ahmed-nazir/Capstone/docs/Design/SystDesign/Electrical_Schematic.png

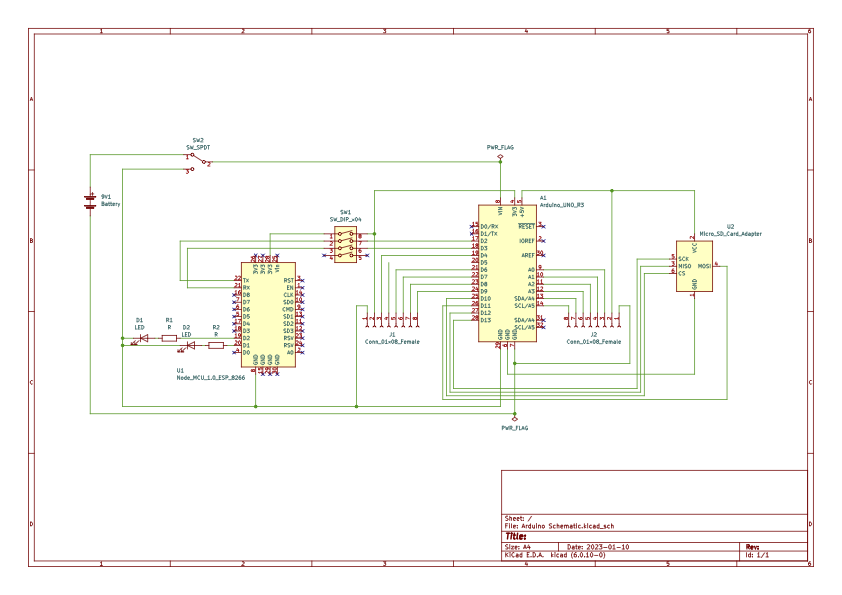
docs/Design/SystDesign/Electrical_Schematic.png
