ahmed-nazir/Capstone/docs/Design/SystDesign/GUI_designer.png

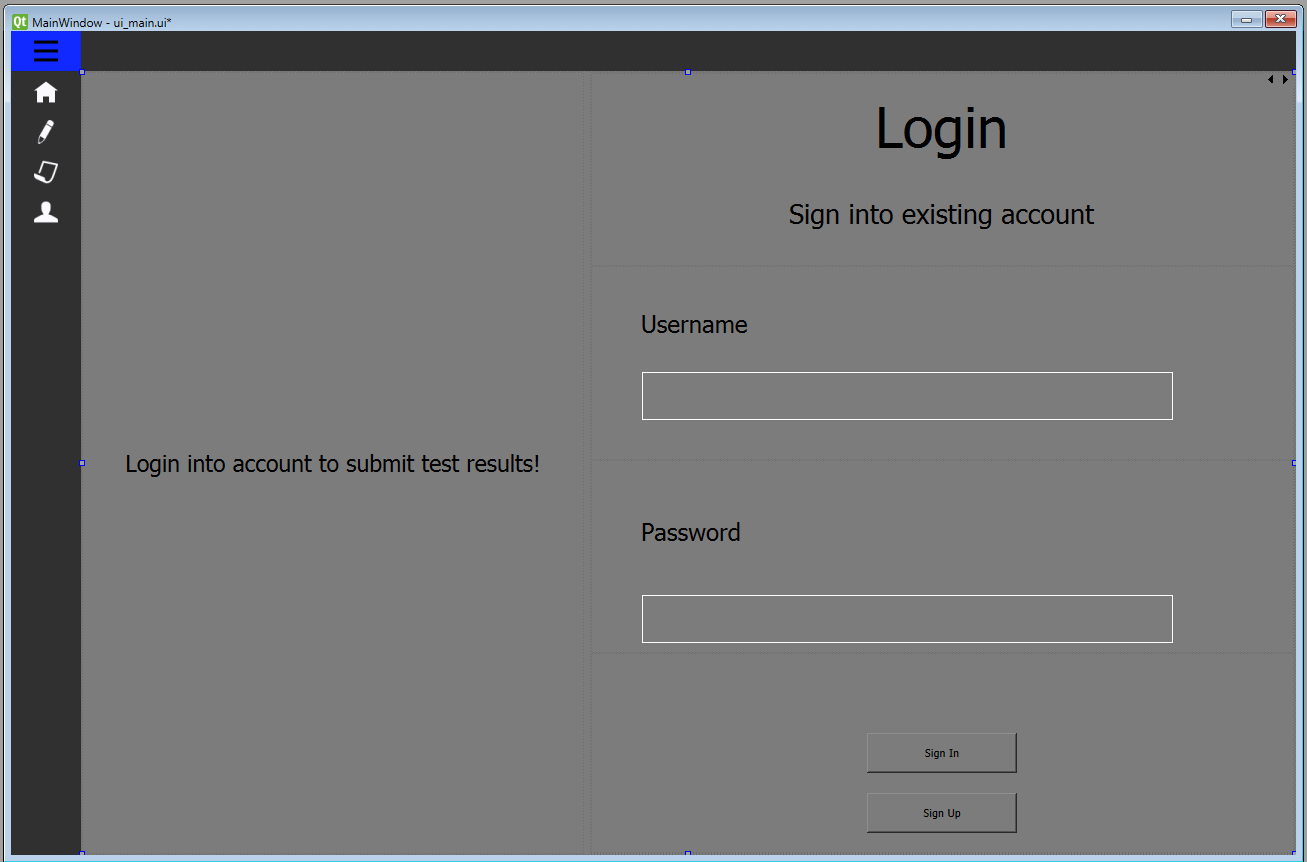
docs/Design/SystDesign/GUI_designer.png
