ahmed-nazir/Capstone/docs/Design/SystDesign/GUI_sketch.png

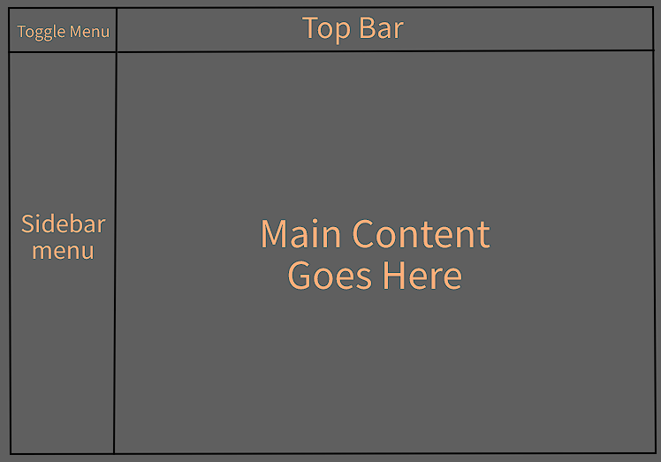
docs/Design/SystDesign/GUI_sketch.png
