ahmed-nazir/Capstone/docs/Design/SystDesign/PCB_Schematic.png

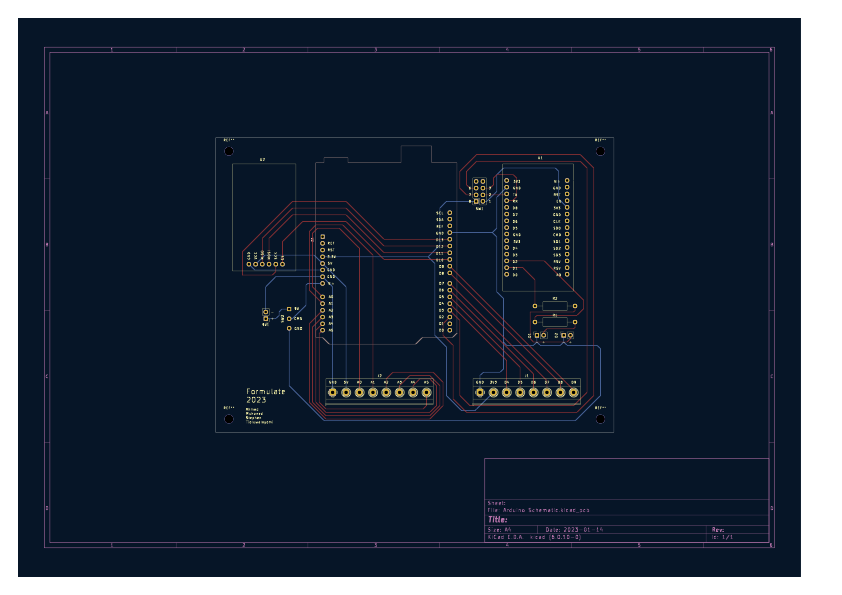
docs/Design/SystDesign/PCB_Schematic.png
