ahmed-nazir/Capstone/docs/SRS/functional_decomposition.png

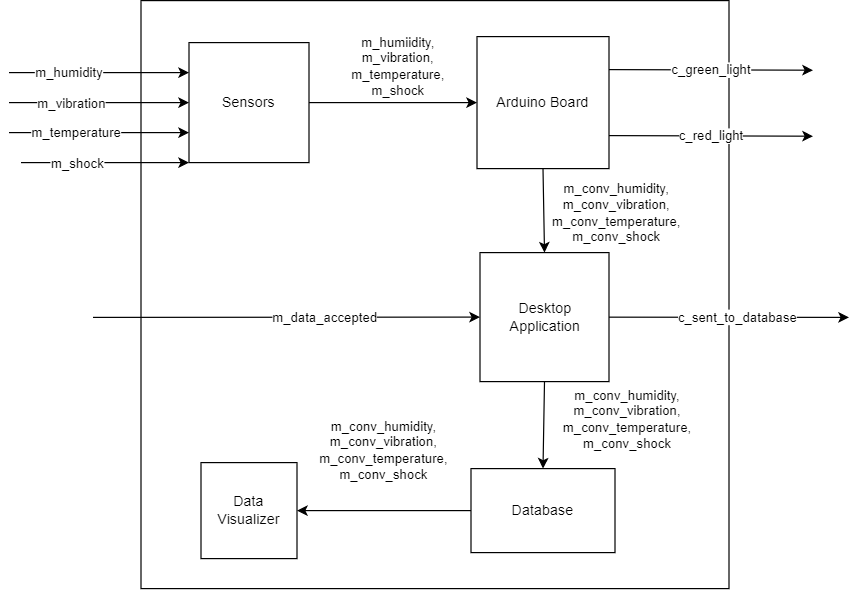
docs/SRS/functional_decomposition.png
