ahmed-nazir/Capstone/docs/VnVReport/Latency_Data.png

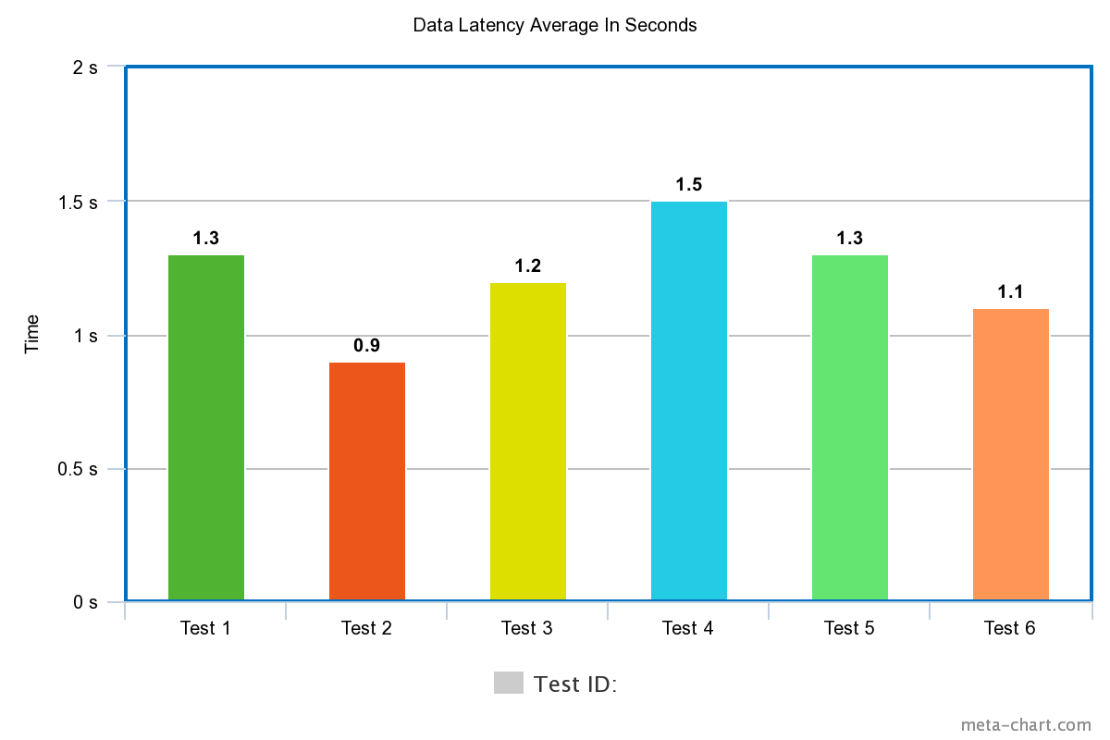
docs/VnVReport/Latency_Data.png
