ahmed-nazir/Capstone/test/Formulate Image.jpg

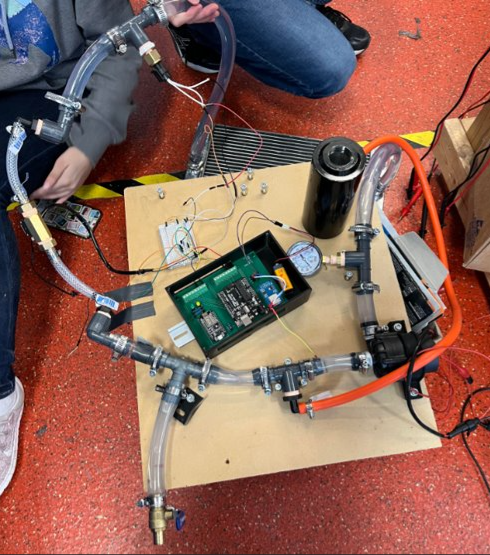
test/Formulate Image.jpg
