ahmed-nazir/Capstone/src/Electrical/REV 0/Electrical Schematic.pdf

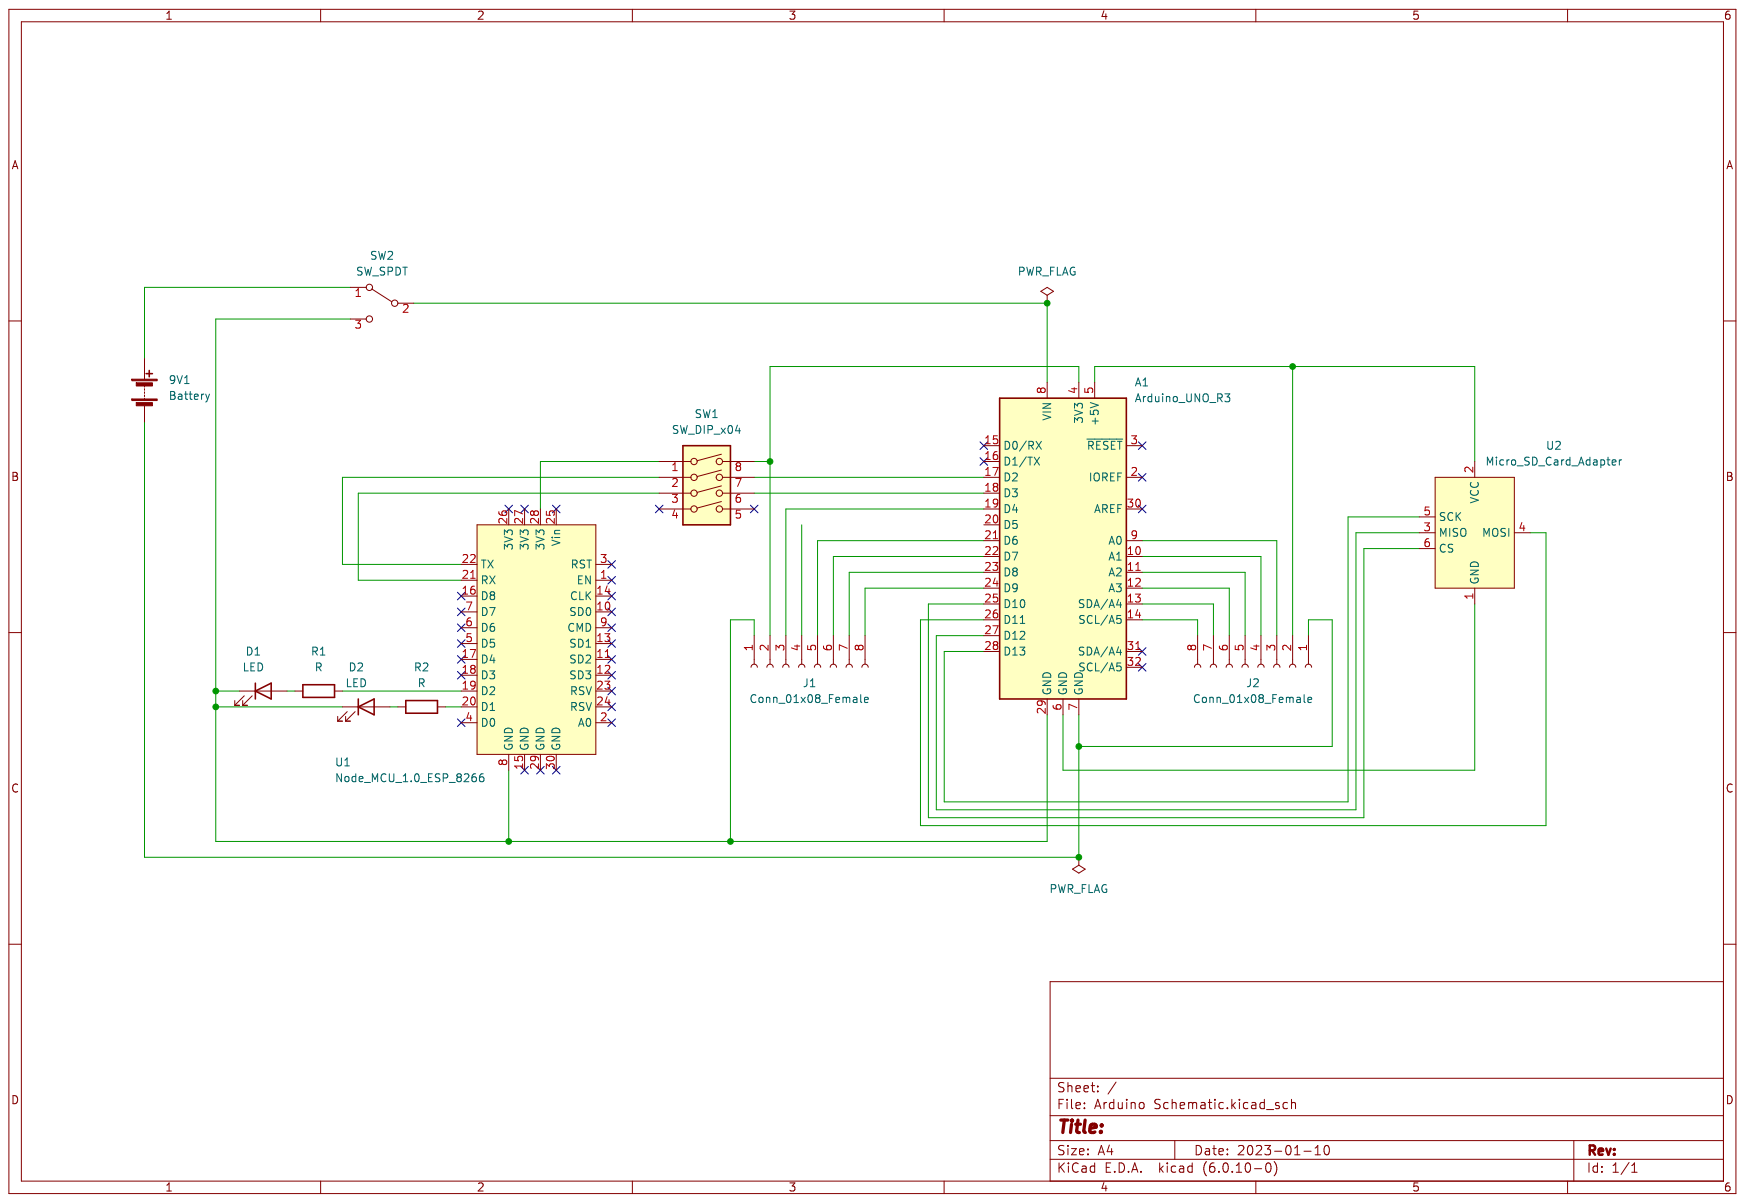
[picture p46: page 1]
