ahmed-nazir/Capstone/src/Electrical/REV 0/PCB Schematic.pdf

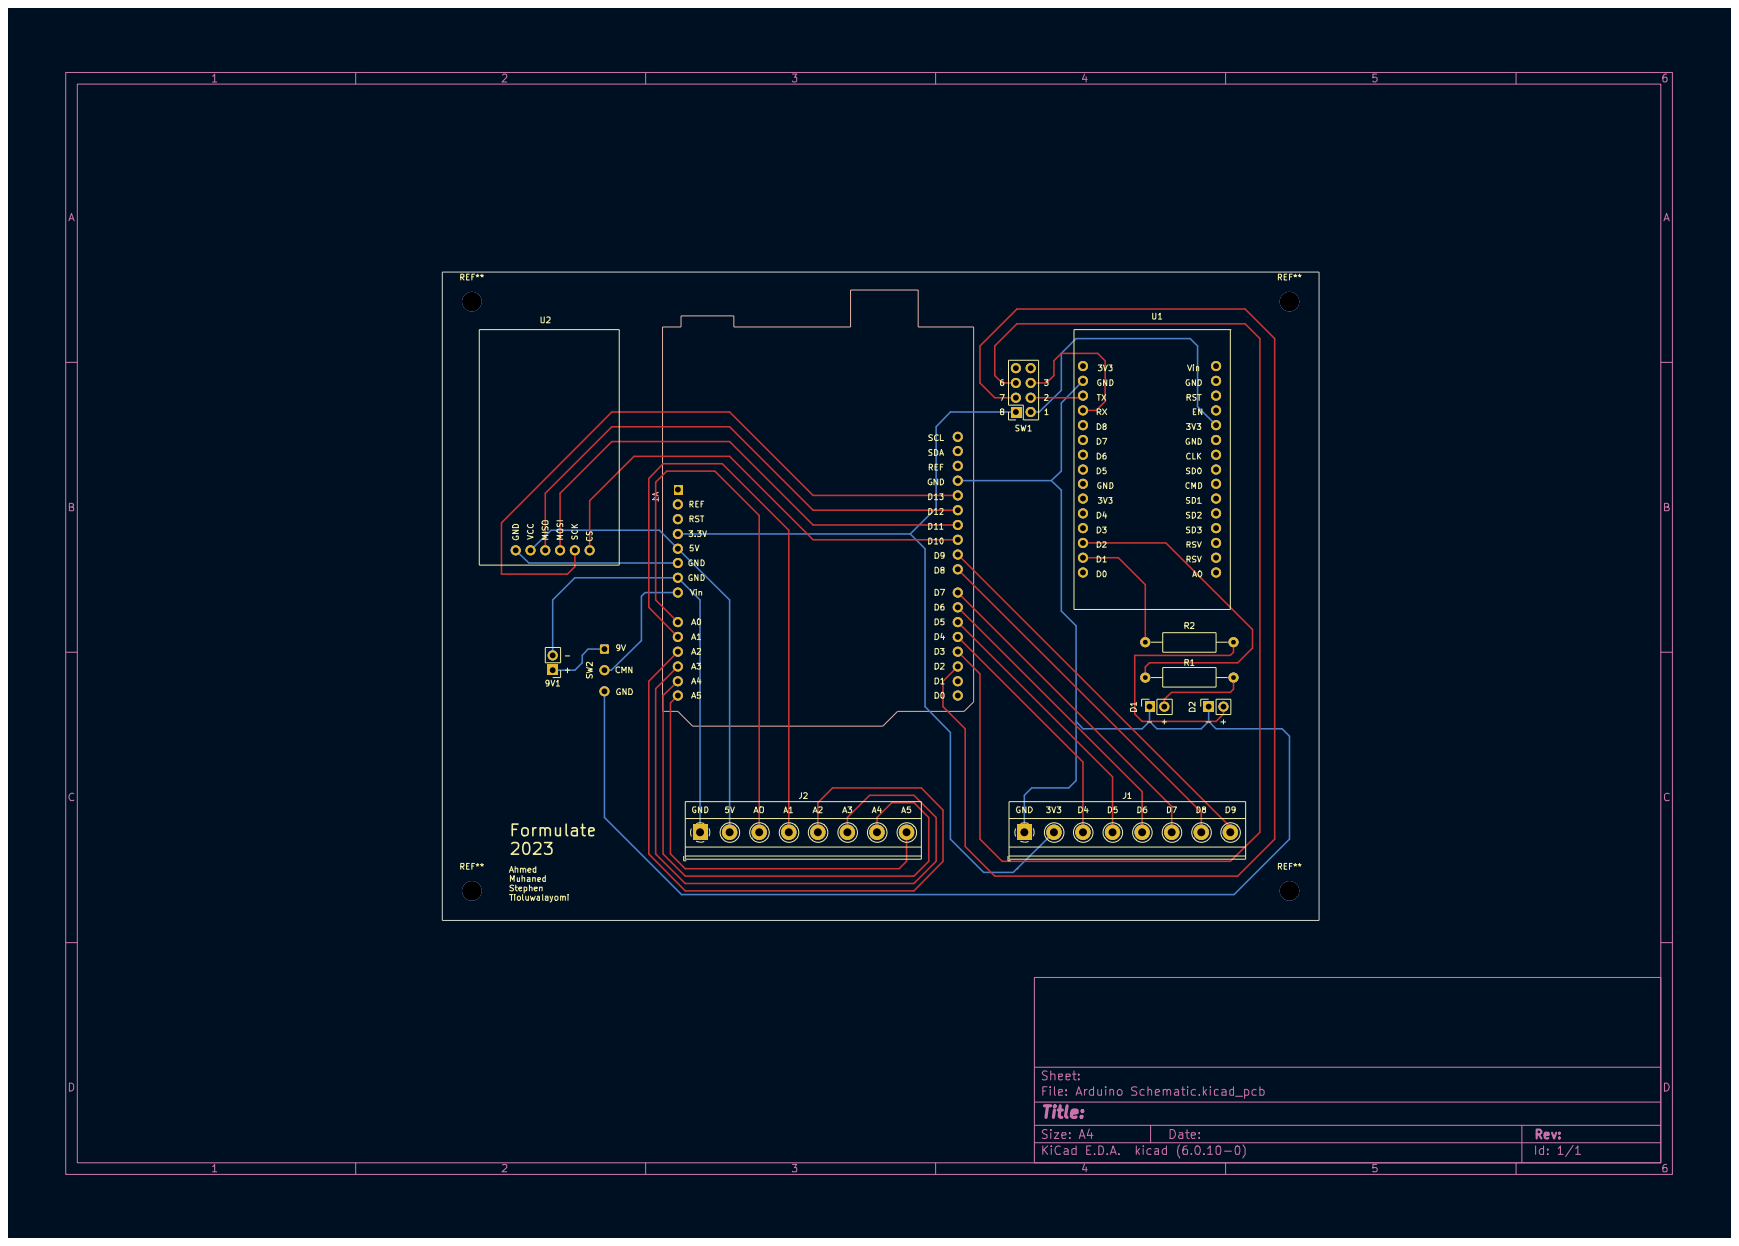
[picture p47: page 1]
